Annex-Engineering/Sherpa-Extruder/Tall_Direct_Drive_Variant/STLs/housing_rear_x1_rev1.stl

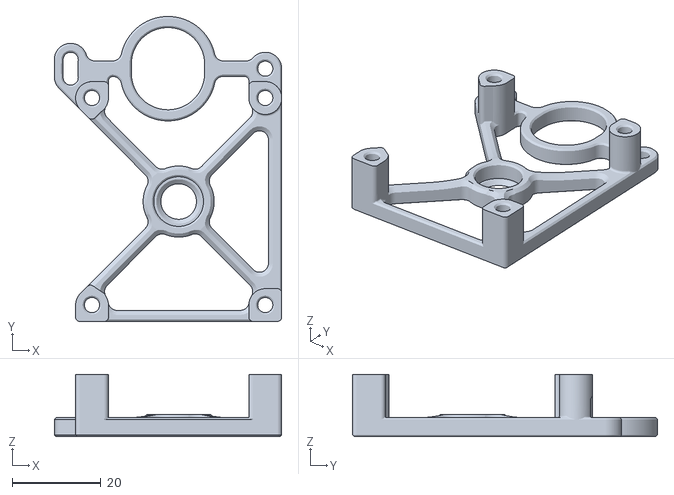
[picture p19: CAD file, 2020-04-29]
Tall_Direct_Drive_Variant/STLs/housing_rear_x1_rev1.stl
51.2 x 68.6 x 14.0
