Annex-Engineering/Sherpa-Extruder/Toolheads/VORON_2.2/voron_30mm_skeeter_sherpa_tall/stls/30mm_skeeter_toolhead_x1_rev2.stl

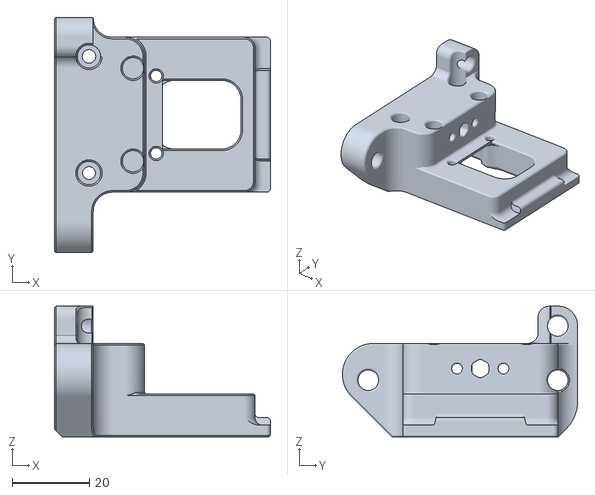
[picture p20: CAD file, 2020-06-04]
Toolheads/VORON_2.2/voron_30mm_skeeter_sherpa_tall/stls/30mm_skeeter_toolhead_x1_rev2.stl
55.8 x 60.7 x 33.7
