Annex-Engineering/Sherpa-Extruder/Toolheads/VORON_2.2/voron_40mm_skeeter_sherpa_tall/stl/[a]_40mm_skeeter_duct_spacer_x1_rev1.stl

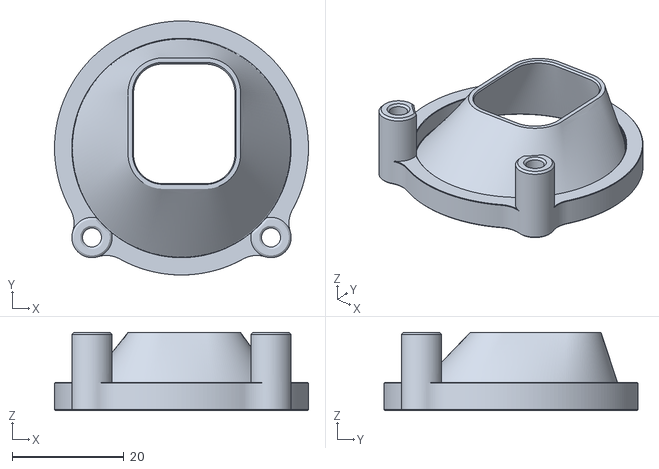
[picture p21: CAD file, 2020-06-04]
Toolheads/VORON_2.2/voron_40mm_skeeter_sherpa_tall/stl/[a]_40mm_skeeter_duct_spacer_x1_rev1.stl
45.4 x 45.4 x 14.0
