Annex-Engineering/Sherpa-Extruder/Tools/STLs/gear_shaft_pressing_tool_base_x1_rev1.stl

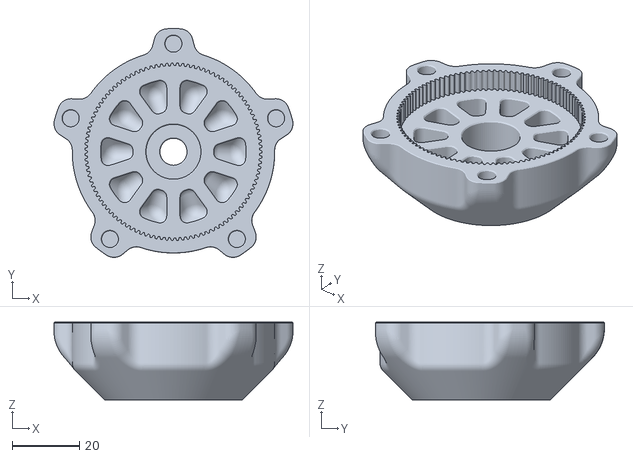
[picture p22: CAD file, 2020-04-30]
Tools/STLs/gear_shaft_pressing_tool_base_x1_rev1.stl
70.8 x 67.8 x 23.0
