Annex-Engineering/Sherpa-Extruder/Folded_Variant/STLs/85t_rounded_spur_gear_0.5mm_flat_x1_rev1.stl

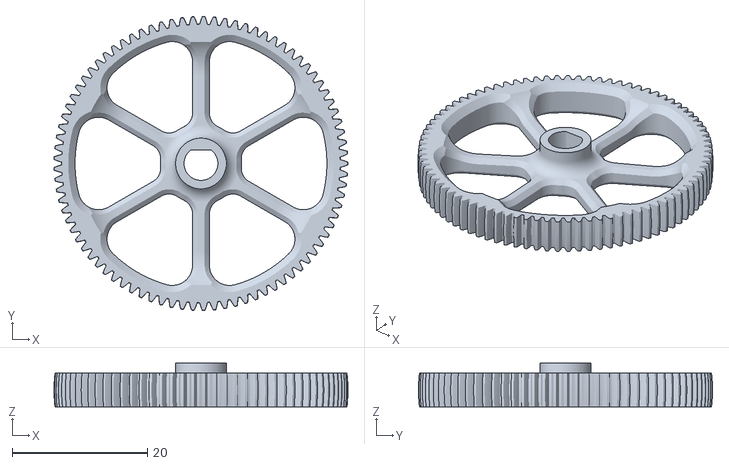
[picture p23: CAD file, 2020-08-25]
Folded_Variant/STLs/85t_rounded_spur_gear_0.5mm_flat_x1_rev1.stl
43.5 x 43.5 x 6.50
