Annex-Engineering/Sherpa-Extruder/Tall_Bowden_Variant/STLs/rappel_adapter_x1_rev1.stl

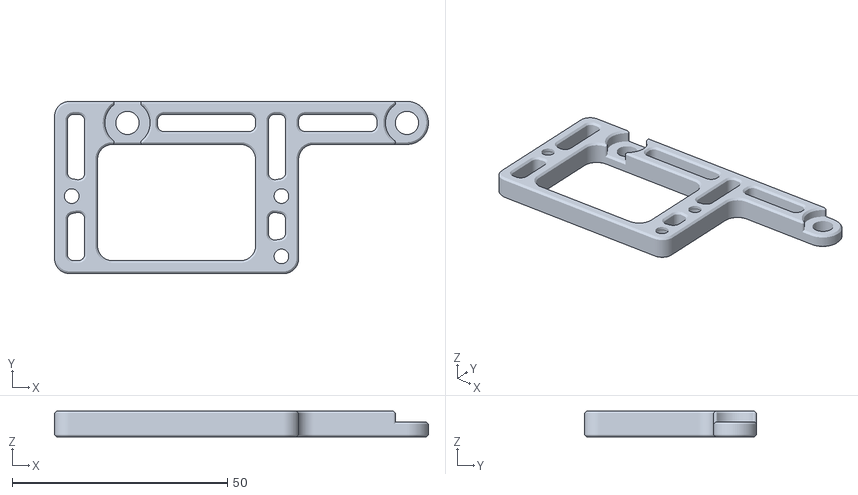
[picture p24: CAD file, 2020-04-29]
Tall_Bowden_Variant/STLs/rappel_adapter_x1_rev1.stl
86.9 x 40.0 x 6.00
