Annex-Engineering/Sherpa-Extruder/Tall_Direct_Drive_Variant/STLs/housing_front_x1_rev1.stl

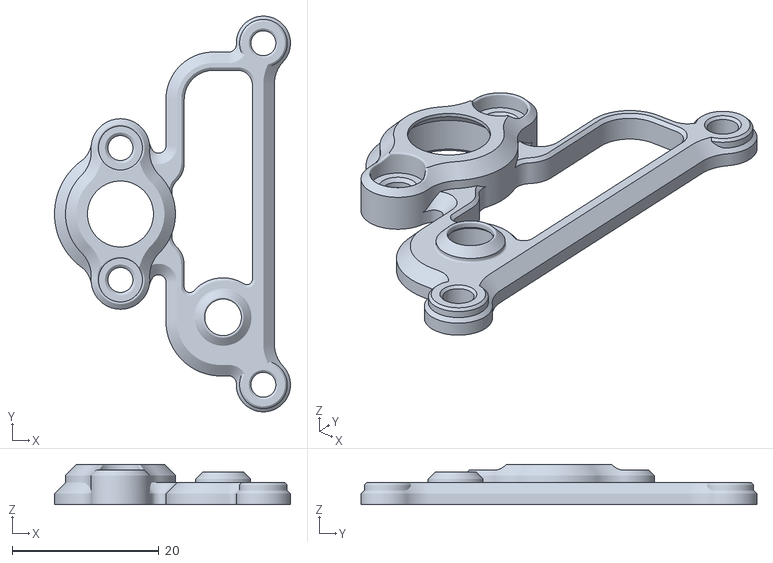
[picture p25: CAD file, 2020-04-29]
Tall_Direct_Drive_Variant/STLs/housing_front_x1_rev1.stl
32.2 x 54.0 x 5.50
