Annex-Engineering/Sherpa-Extruder/Toolheads/VORON_2.2/voron_30mm_skeeter_sherpa_tall/stls/30mm_skeeter_fan_holder_x1_rev1.stl

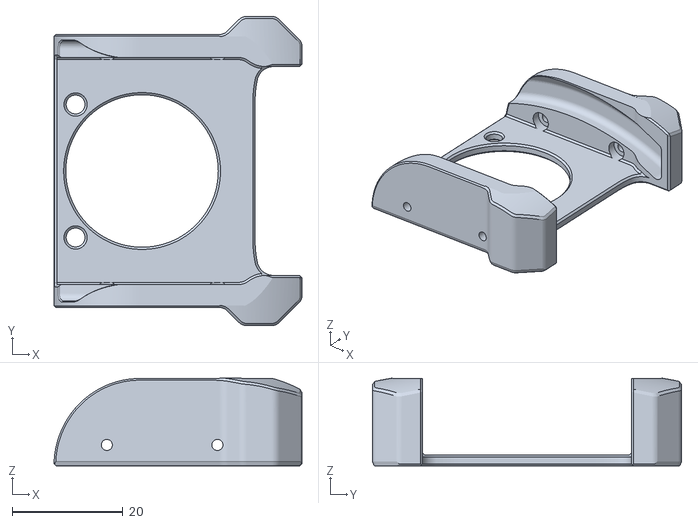
[picture p26: CAD file, 2020-06-04]
Toolheads/VORON_2.2/voron_30mm_skeeter_sherpa_tall/stls/30mm_skeeter_fan_holder_x1_rev1.stl
44.8 x 55.8 x 15.9
