Annex-Engineering/Sherpa-Extruder/Toolheads/VORON_2.2/voron_40mm_dragon_sherpa_tall/stls/40mm_dragon_toolhead_x1_rev1.stl

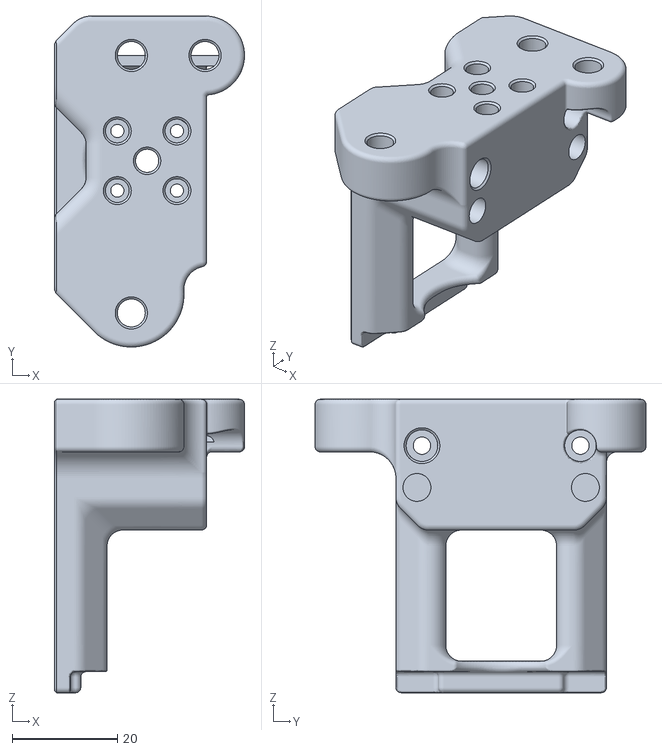
[picture p27: CAD file, 2020-06-04]
Toolheads/VORON_2.2/voron_40mm_dragon_sherpa_tall/stls/40mm_dragon_toolhead_x1_rev1.stl
36.1 x 62.9 x 55.8
