Annex-Engineering/Sherpa-Extruder/Folded_Variant/STLs/idler_carrier_x1_rev1.stl

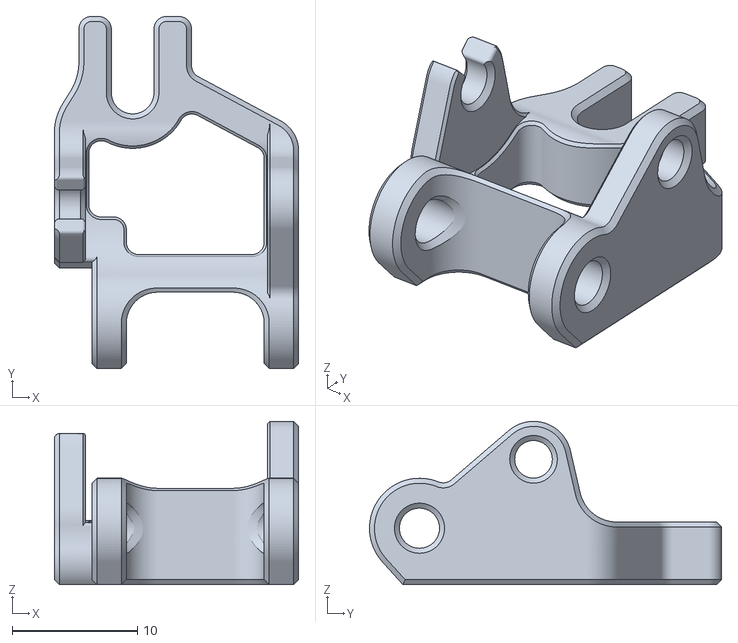
[picture p28: CAD file, 2020-08-25]
Folded_Variant/STLs/idler_carrier_x1_rev1.stl
19.5 x 28.1 x 13.0
