Annex-Engineering/Sherpa-Extruder/Tall_Bowden_Variant/STLs/housing_core_bowden_x1_rev1.stl

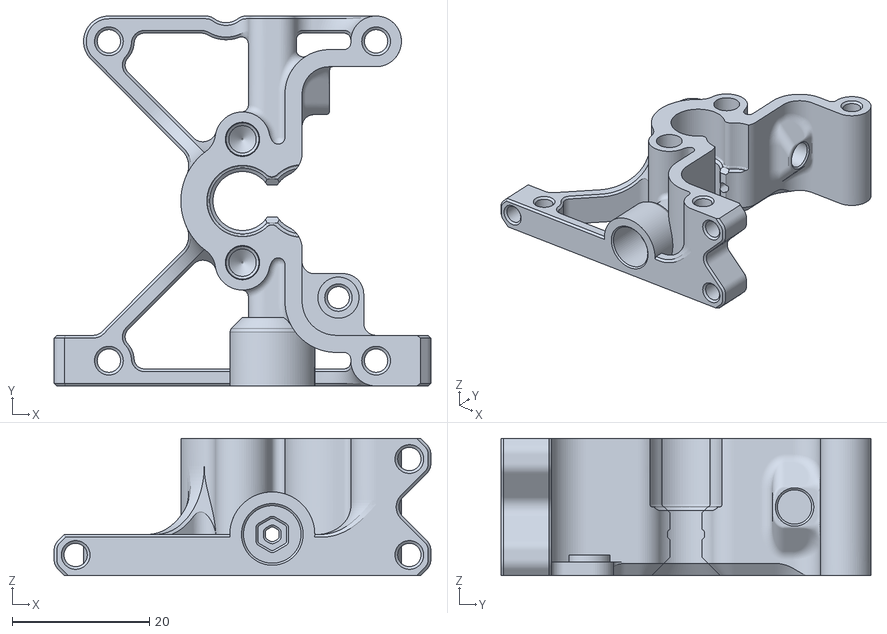
[picture p29: CAD file, 2020-04-29]
Tall_Bowden_Variant/STLs/housing_core_bowden_x1_rev1.stl
55.0 x 54.0 x 20.0
