Annex-Engineering/Sherpa-Extruder/Toolheads/VORON_2.2/voron_40mm_dragon_sherpa_tall/stls/[a]_40mm_dragon_duct_spacer_x1_rev1.stl

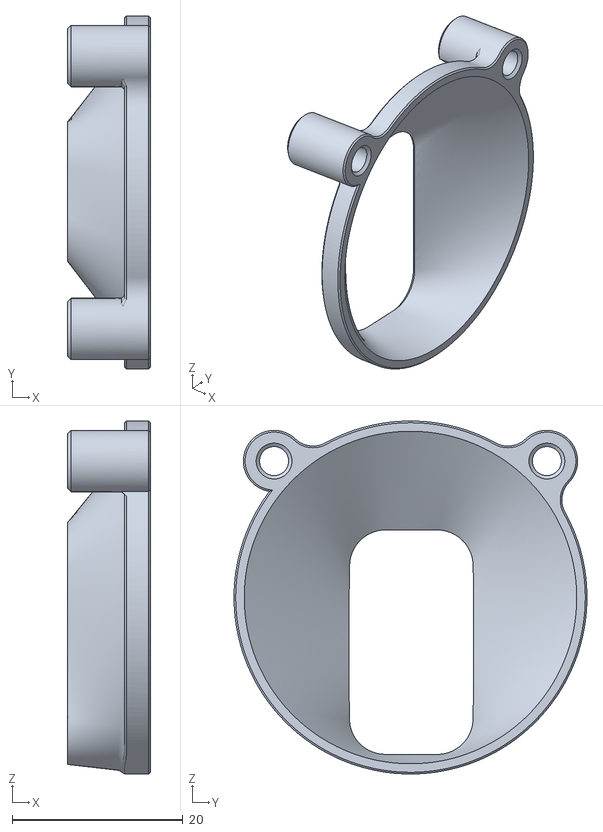
[picture p30: CAD file, 2020-06-04]
Toolheads/VORON_2.2/voron_40mm_dragon_sherpa_tall/stls/[a]_40mm_dragon_duct_spacer_x1_rev1.stl
9.69 x 41.4 x 41.4
