Annex-Engineering/Sherpa-Extruder/Folded_Variant/STLs/housing_core_bowden_x1_rev1.stl

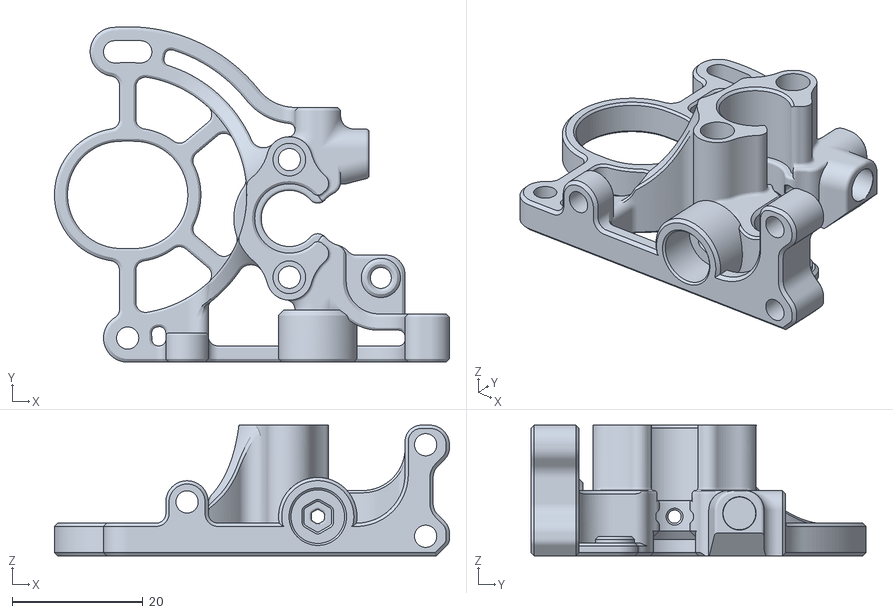
[picture p32: CAD file, 2020-08-25]
Folded_Variant/STLs/housing_core_bowden_x1_rev1.stl
60.4 x 51.3 x 20.0
