Annex-Engineering/Sherpa-Extruder/Tall_Bowden_Variant/STLs/[a}_nema16_17_adapter_plate_7mm_x1_rev1.stl

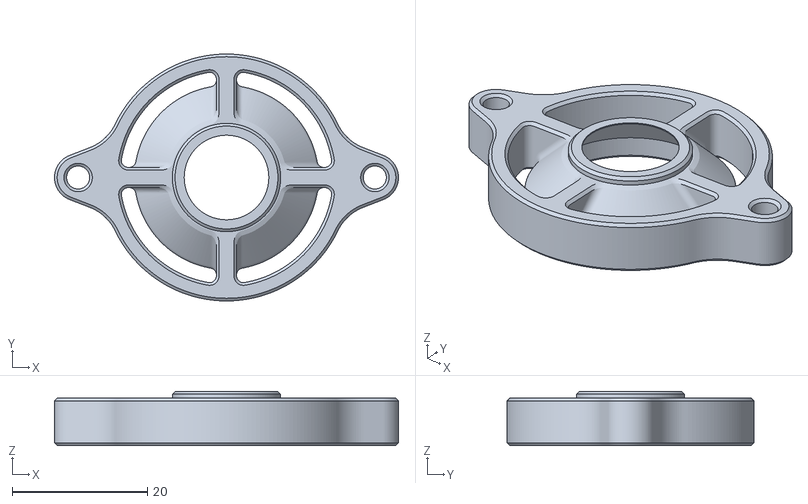
[picture p33: CAD file, 2020-04-29]
Tall_Bowden_Variant/STLs/[a}_nema16_17_adapter_plate_7mm_x1_rev1.stl
50.8 x 36.5 x 8.00
