Annex-Engineering/Sherpa-Extruder/Tall_Direct_Drive_Variant/STLs/housing_core_dd_x1_rev1.stl

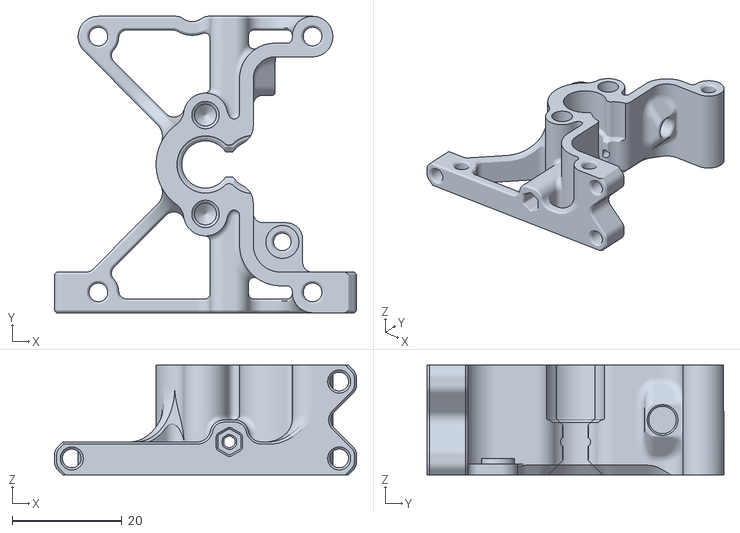
[picture p34: CAD file, 2020-04-29]
Tall_Direct_Drive_Variant/STLs/housing_core_dd_x1_rev1.stl
55.0 x 54.0 x 20.0
