Annex-Engineering/Sherpa-Extruder/Folded_Variant/STLs/rear_bearing_retainer_x1_rev1.stl

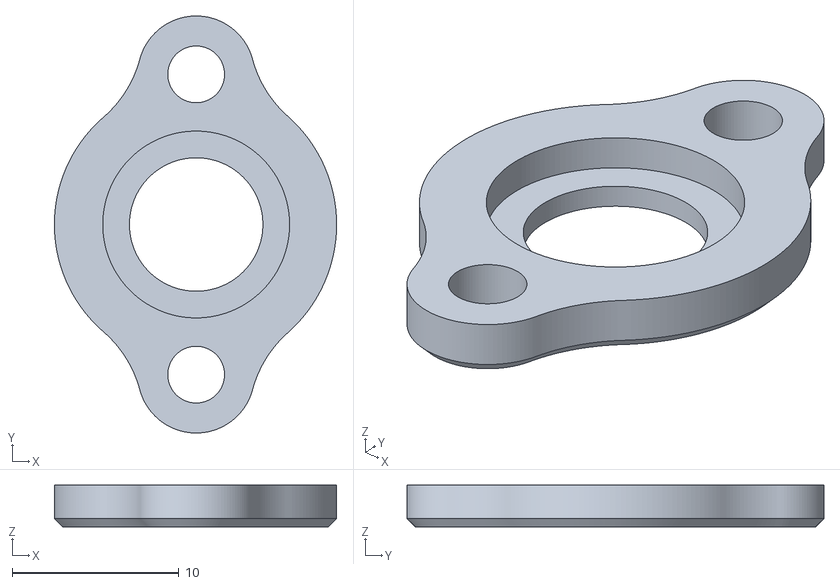
[picture p35: CAD file, 2020-08-25]
Folded_Variant/STLs/rear_bearing_retainer_x1_rev1.stl
16.9 x 25.0 x 2.50
