Annex-Engineering/Sherpa-Extruder/Tall_Direct_Drive_Variant/STLs/nema14_spacer_4mm_x1_rev1.stl

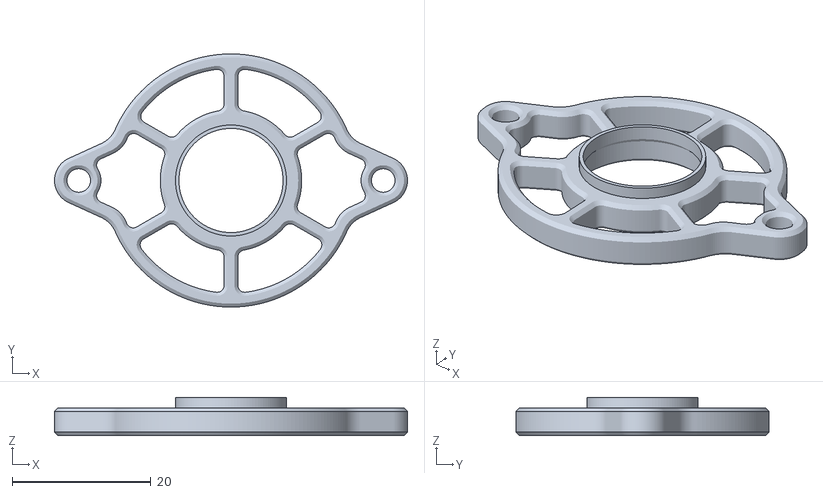
[picture p37: CAD file, 2020-04-29]
Tall_Direct_Drive_Variant/STLs/nema14_spacer_4mm_x1_rev1.stl
50.9 x 36.5 x 5.50
